mcmn13/UselessBox/Photos/10.jpg

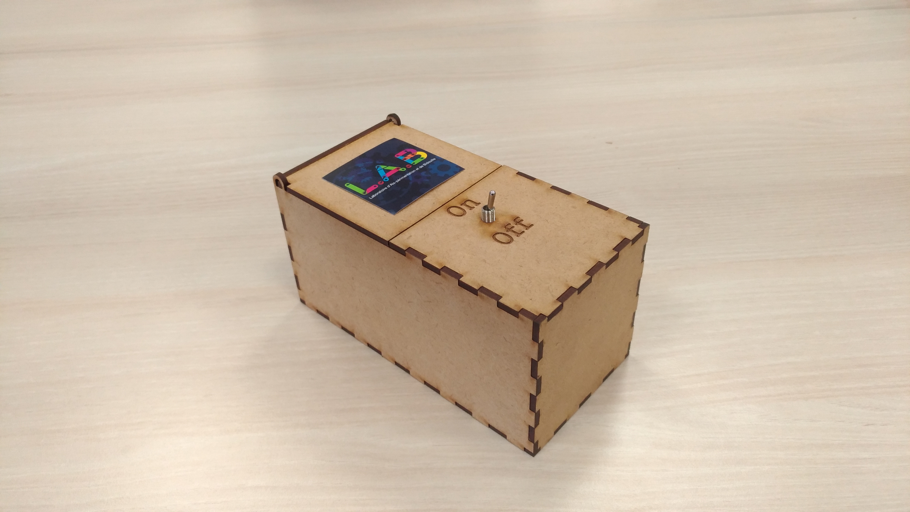
Photos/10.jpg
