mcmn13/UselessBox/Photos/11.jpg

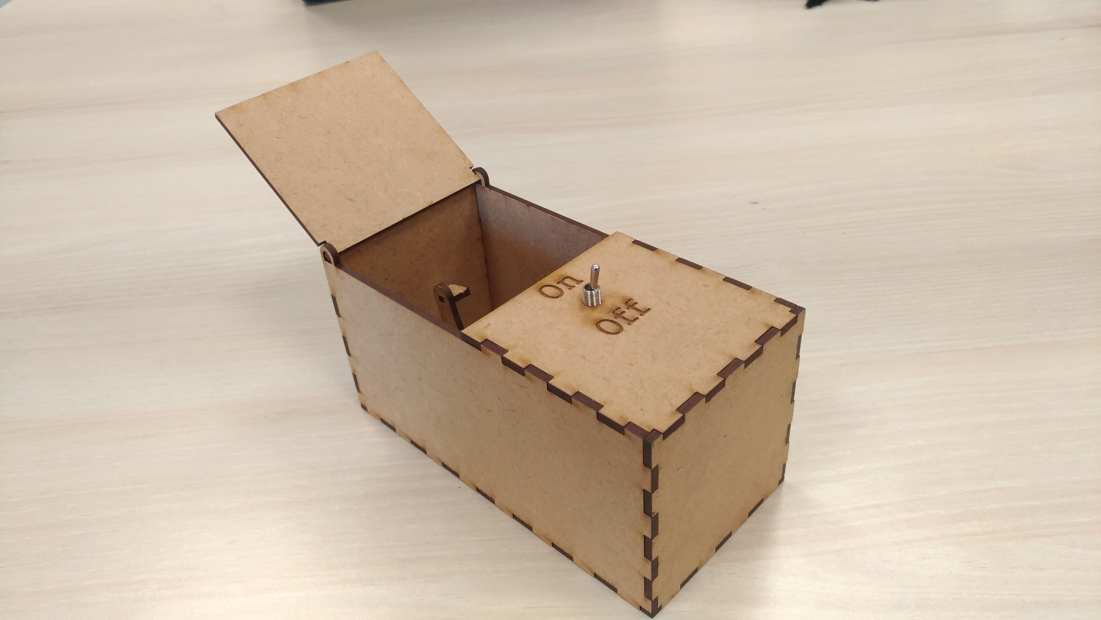
Photos/11.jpg
