mcmn13/UselessBox/Photos/12.jpg

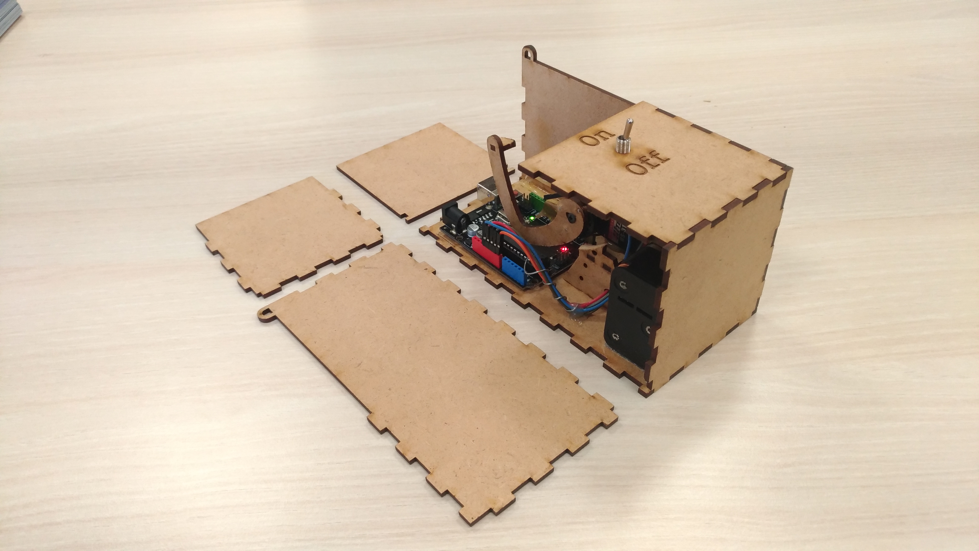
Photos/12.jpg
