mcmn13/UselessBox/Photos/gif/v2/P_20171027_152719_vHDR_On.jpg

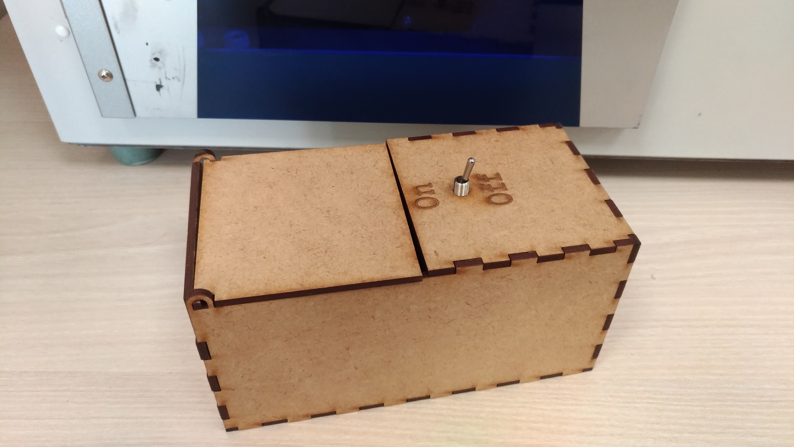
Photos/gif/v2/P_20171027_152719_vHDR_On.jpg
