mcmn13/UselessBox/Photos/gif/v2/P_20171027_152738_vHDR_On.jpg

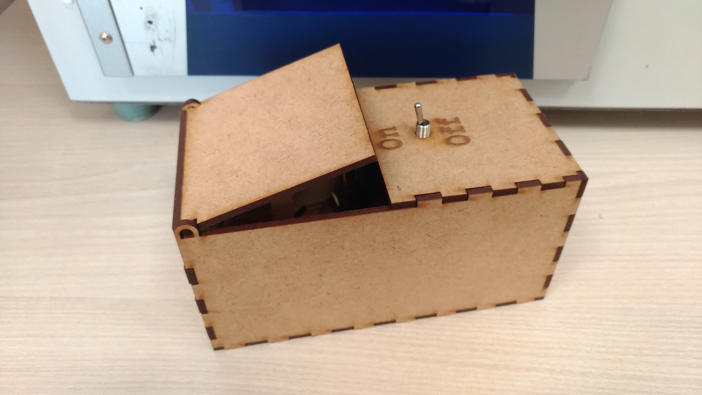
Photos/gif/v2/P_20171027_152738_vHDR_On.jpg
