mcmn13/UselessBox/Photos/Illustration.jpg

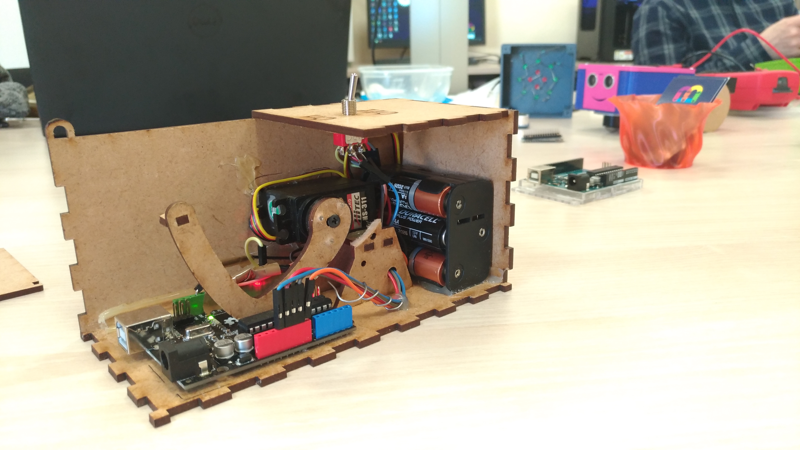
Photos/Illustration.jpg
